marcocipriani01/Anycubic-Mega-mods/E3D Hemera and TriangleLab Matrix X-carriage/40mm fan grid.stl

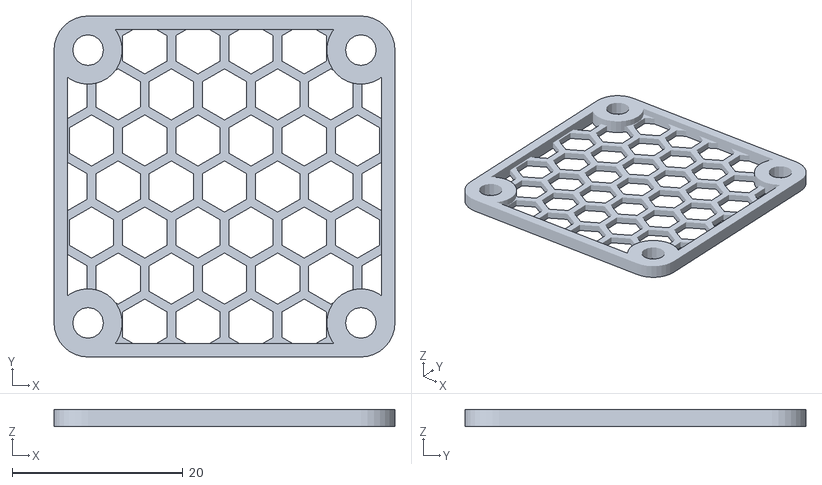
[picture p16: CAD file, 2021-07-02]
E3D Hemera and TriangleLab Matrix X-carriage/40mm fan grid.stl
40.0 x 40.0 x 2.00
