marcocipriani01/Anycubic-Mega-mods/Filament holder with bearings/Filament holder with 608 bearings.step

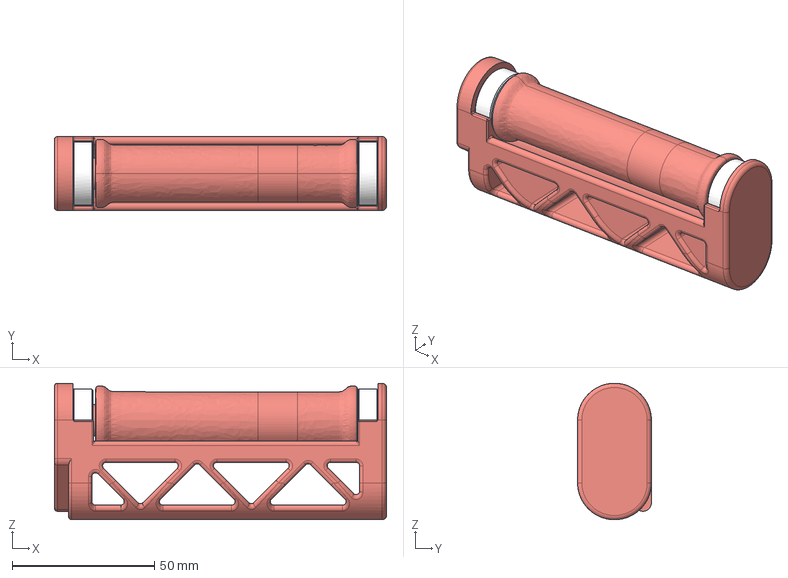
[picture p17: CAD file, 2021-07-02]
Filament holder with bearings/Filament holder with 608 bearings.step
116.8 x 26.0 x 48.0 mm
5972K91 x 2
ReelSTEP_1of4 v4
BearinPinSTEP_2of4 v2
