marcocipriani01/Anycubic-Mega-mods/Improved X axis/Pulley slider.stl

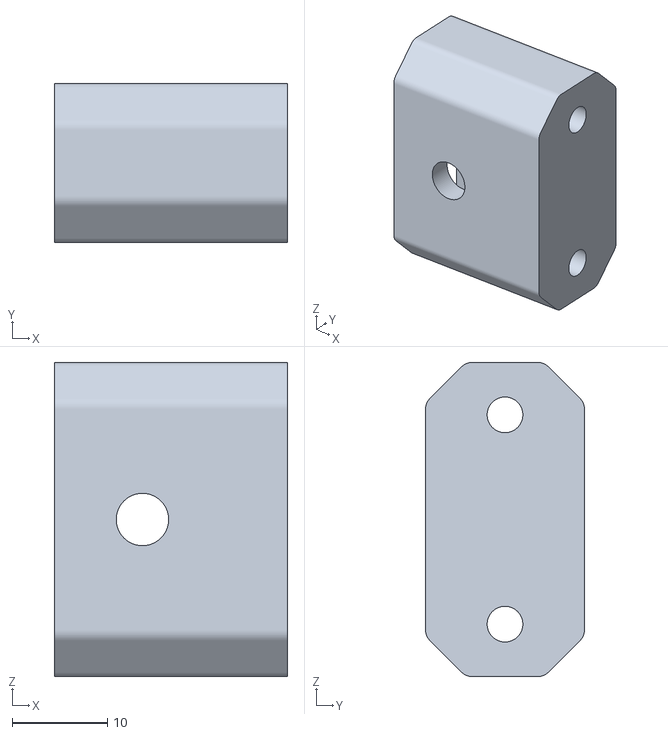
[picture p18: CAD file, 2022-04-29]
Improved X axis/Pulley slider.stl
24.5 x 16.7 x 33.0
