marcocipriani01/Anycubic-Mega-mods/E3D Hemera and TriangleLab Matrix X-carriage/Cooling fan duct.stl

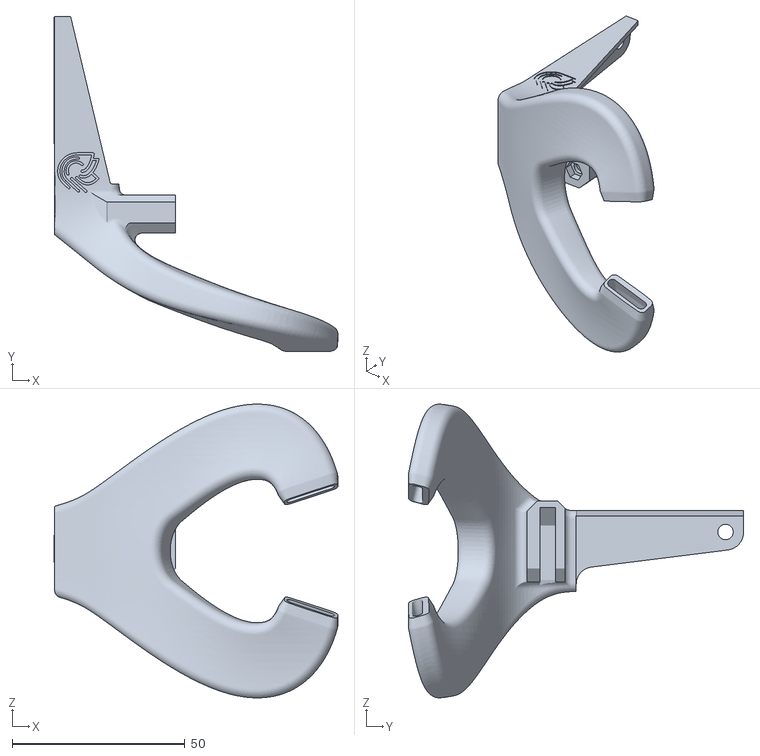
[picture p19: CAD file, 2021-07-02]
E3D Hemera and TriangleLab Matrix X-carriage/Cooling fan duct.stl
82.3 x 97.1 x 85.1
