marcocipriani01/Anycubic-Mega-mods/Filament holder with bearings/Filament holder with 608 bearings - bearing pin.stl

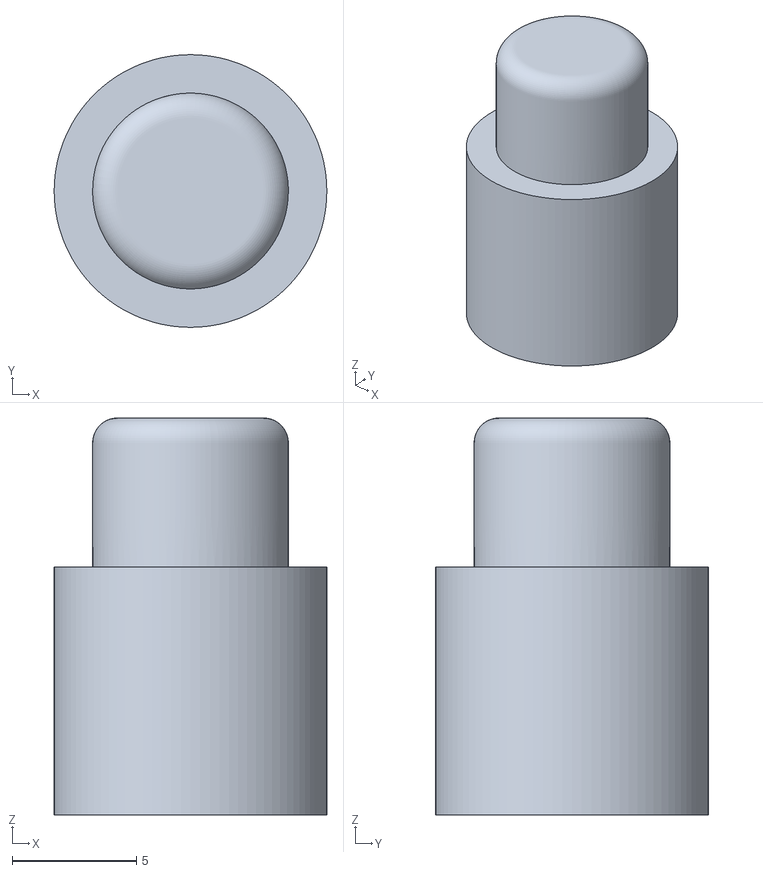
[picture p20: CAD file, 2021-07-02]
Filament holder with bearings/Filament holder with 608 bearings - bearing pin.stl
11.0 x 11.0 x 16.0
