marcocipriani01/Anycubic-Mega-mods/Improved X axis/X axis slider - right.stl

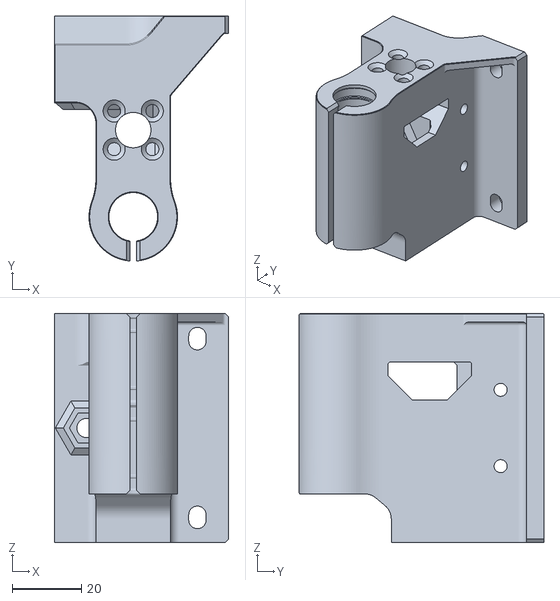
[picture p21: CAD file, 2022-04-29]
Improved X axis/X axis slider - right.stl
50.2 x 70.6 x 66.0
