marcocipriani01/Anycubic-Mega-mods/E3D Hemera and TriangleLab Matrix X-carriage/Cable chain support.stl

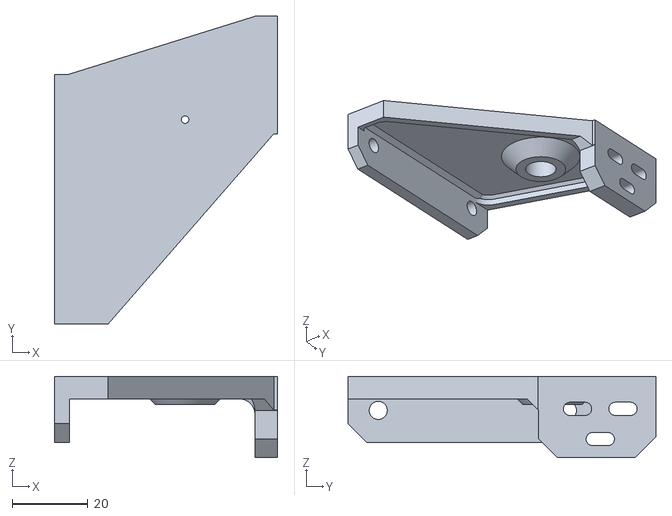
[picture p22: CAD file, 2021-07-02]
E3D Hemera and TriangleLab Matrix X-carriage/Cable chain support.stl
59.0 x 81.4 x 21.5
