marcocipriani01/Anycubic-Mega-mods/Klipper/hacks.cfg

# Klipper hacks and workarounds

# Arduino aliases for atmega2560/1280 (Arduino mega) boards
[board_pins arduino-mega]
aliases:
    ar0=PE0, ar1=PE1, ar2=PE4, ar3=PE5, ar4=PG5,
    ar5=PE3, ar6=PH3, ar7=PH4, ar8=PH5, ar9=PH6,
    ar10=PB4, ar11=PB5, ar12=PB6, ar13=PB7, ar14=PJ1,
    ar15=PJ0, ar16=PH1, ar17=PH0, ar18=PD3, ar19=PD2,
    ar20=PD1, ar21=PD0, ar22=PA0, ar23=PA1, ar24=PA2,
    ar25=PA3, ar26=PA4, ar27=PA5, ar28=PA6, ar29=PA7,
    ar30=PC7, ar31=PC6, ar32=PC5, ar33=PC4, ar34=PC3,
    ar35=PC2, ar36=PC1, ar37=PC0, ar38=PD7, ar39=PG2,
    ar40=PG1, ar41=PG0, ar42=PL7, ar43=PL6, ar44=PL5,
    ar45=PL4, ar46=PL3, ar47=PL2, ar48=PL1, ar49=PL0,
    ar50=PB3, ar51=PB2, ar52=PB1, ar53=PB0, ar54=PF0,
    ar55=PF1, ar56=PF2, ar57=PF3, ar58=PF4, ar59=PF5,
    ar60=PF6, ar61=PF7, ar62=PK0, ar63=PK1, ar64=PK2,
    ar65=PK3, ar66=PK4, ar67=PK5, ar68=PK6, ar69=PK7,
    analog0=PF0, analog1=PF1, analog2=PF2, analog3=PF3, analog4=PF4,
    analog5=PF5, analog6=PF6, analog7=PF7, analog8=PK0, analog9=PK1,
    analog10=PK2, analog11=PK3, analog12=PK4, analog13=PK5, analog14=PK6,
    analog15=PK7,
    # Marlin adds these additional aliases
    ml70=PG4, ml71=PG3, ml72=PJ2, ml73=PJ3, ml74=PJ7,
    ml75=PJ4, ml76=PJ5, ml77=PJ6, ml78=PE2, ml79=PE6,
    ml80=PE7, ml81=PD4, ml82=PD5, ml83=PD6, ml84=PH2,
    ml85=PH7

# Change filament
[pause_resume]

[respond]
default_type: echo
default_prefix: echo:

[gcode_macro M300]
gcode:
    {% set s = params.S|default(1000)|float %}
    {% set p = params.P|default(100)|float %}
    SET_PIN PIN=buzzer_pin VALUE={s}
    G4 P{p}
    SET_PIN PIN=buzzer_pin VALUE=0

[idle_timeout]
gcode:
    TURN_OFF_HEATERS
    M107
    M84
timeout: 500

[force_move]
enable_force_move: True

[gcode_macro FORCE_MOVE_POS]
gcode:
  SET_KINEMATIC_POSITION X=100 Y=100 Z=100

[virtual_sdcard]
path: ~/klipper_gcodes

[gcode_arcs]

[display_status]

[save_variables]
filename: ~/klipper_config/variables.cfg

[gcode_macro SET_GCODE_OFFSET]
rename_existing: _SET_GCODE_OFFSET
gcode:
    {% if printer.save_variables.variables.gcode_offsets %}
        {% set offsets = printer.save_variables.variables.gcode_offsets %}
    {% else %} 
        {% set offsets = {'x': None,'y': None,'z': None} %}
    {% endif %}
    {% set ns = namespace(offsets={'x': offsets.x,'y': offsets.y,'z': offsets.z}) %}
    _SET_GCODE_OFFSET {% for p in params %}{'%s=%s '% (p, params[p])}{% endfor %}
    {%if 'X' in params %}{% set null = ns.offsets.update({'x': params.X}) %}{% endif %}
    {%if 'Y' in params %}{% set null = ns.offsets.update({'y': params.Y}) %}{% endif %}
    {%if 'Z' in params %}{% set null = ns.offsets.update({'z': params.Z}) %}{% endif %}
    {%if 'Z_ADJUST' in params %}
        {%if ns.offsets.z == None %}{% set null = ns.offsets.update({'z': 0}) %}{% endif %}
        {% set null = ns.offsets.update({'z': ns.offsets.z + (params.Z_ADJUST | float)}) %}
    {% endif %}
    SAVE_VARIABLE VARIABLE=gcode_offsets VALUE="{ns.offsets}"

[delayed_gcode BEEP_ON_START]
initial_duration: 1
gcode:
  M300 S299 P200

[delayed_gcode LOAD_GCODE_OFFSETS]
initial_duration: 2
gcode:  
    {% if printer.save_variables.variables.gcode_offsets %}
        {% set offsets = printer.save_variables.variables.gcode_offsets %}
        _SET_GCODE_OFFSET {% for axis, offset in offsets.items() if offsets[axis] %}{ "%s=%s " % (axis, offset) }{% endfor %}
        { action_respond_info("Loaded gcode offsets from saved variables [%s]" % (offsets)) }
    {% endif %}

[verify_heater heater_bed]
max_error: 200
hysteresis: 6
heating_gain: 3

[verify_heater extruder]
max_error: 200
hysteresis: 6
heating_gain: 3
