marcocipriani01/Anycubic-Mega-mods/Klipper/power.cfg

[gcode_macro SHUTDOWN_PRINTER]
gcode:
    {action_call_remote_method("set_device_power", device="Shelly", state="off")}

[delayed_gcode SHUTDOWN_PRINTER_CHECK]
gcode:
    {% if printer.extruder.target == 0.0 and printer.heater_bed.target == 0.0 %}
        {% if printer.extruder.temperature < 80.0 and printer.heater_bed.temperature < 60.0 %}
            UPDATE_DELAYED_GCODE ID=SHUTDOWN_PRINTER_CHECK DURATION=0
            SHUTDOWN_PRINTER
        {% else %}
            UPDATE_DELAYED_GCODE ID=SHUTDOWN_PRINTER_CHECK DURATION=5
        {% endif %}
    {% else %}
        UPDATE_DELAYED_GCODE ID=SHUTDOWN_PRINTER_CHECK DURATION=0
    {% endif %}
